achillecalegari/calegari-view-1/docs/img/07_section_three_quarter.jpg

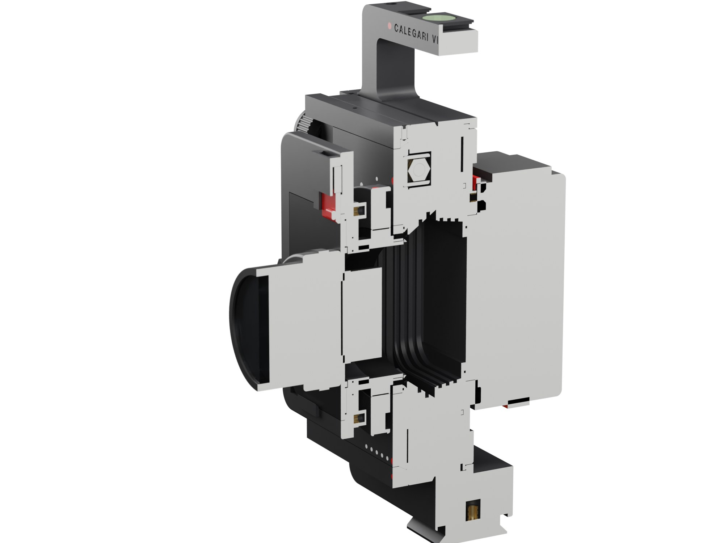
docs/img/07_section_three_quarter.jpg
