achillecalegari/calegari-view-1/print/inlays/x_plate__white.stl

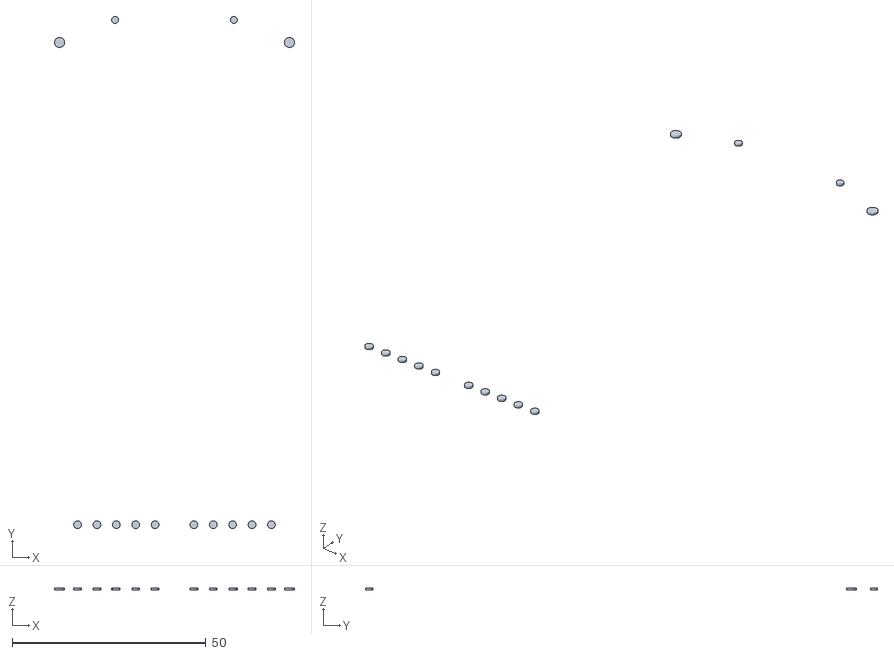
[picture p34: CAD file, 2026-09-28]
print/inlays/x_plate__white.stl
61.9 x 132.1 x 0.6
