achillecalegari/calegari-view-1/print/plates/plate_06_black.3mf

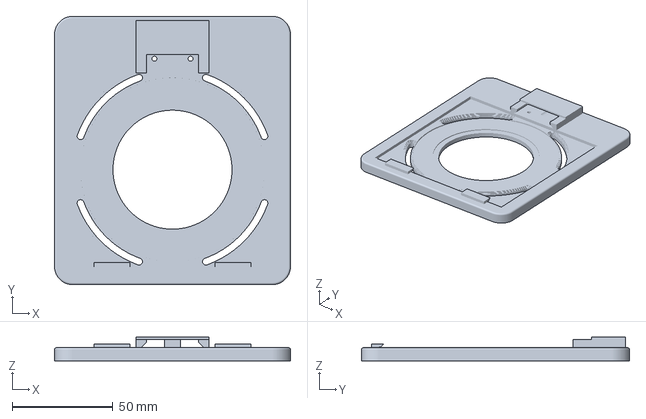
[picture p35: CAD file, 2026-09-28]
print/plates/plate_06_black.3mf
117.0 x 133.0 x 11.7 mm
