achillecalegari/calegari-view-1/print/step/way_y_gib.step

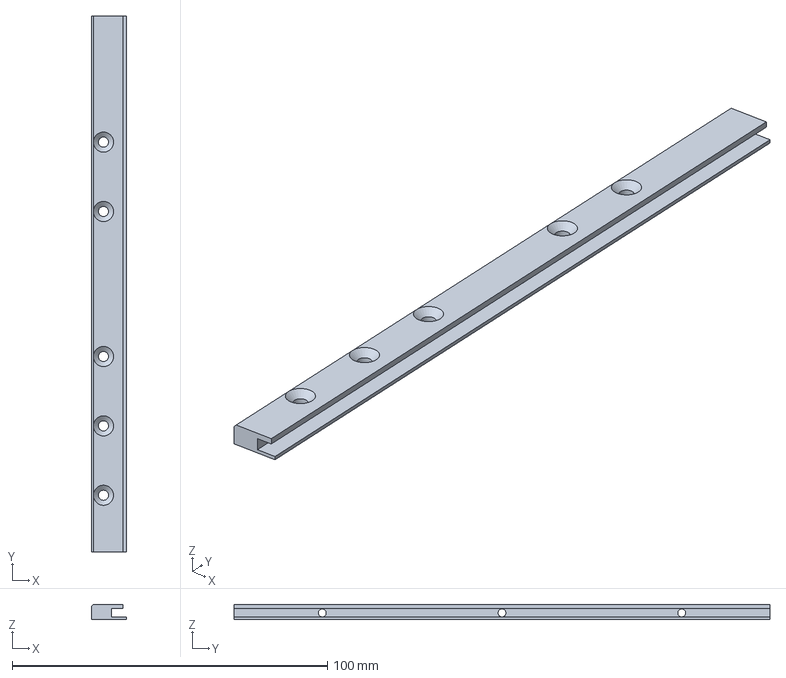
[picture p36: CAD file, 2026-09-28]
print/step/way_y_gib.step
11.0 x 170.0 x 4.80 mm
