achillecalegari/calegari-view-1/print/stl/copal0_shim_0.6mm.stl

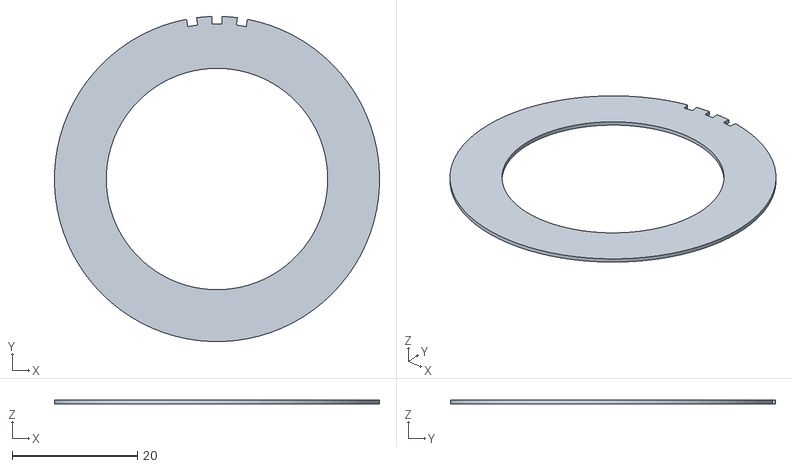
[picture p37: CAD file, 2026-09-27]
print/stl/copal0_shim_0.6mm.stl
52.0 x 52.0 x 0.6
