achillecalegari/calegari-view-1/print/test/coupon_lip_x_bottom.stl

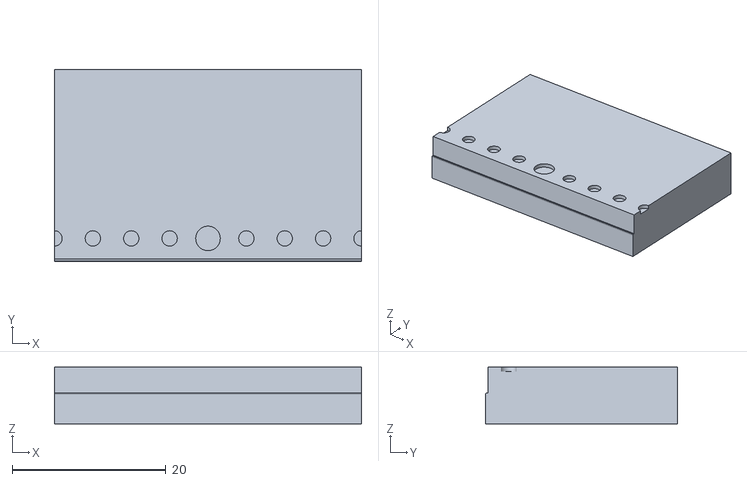
[picture p38: CAD file, 2026-09-28]
print/test/coupon_lip_x_bottom.stl
40.0 x 25.0 x 7.40
