achillecalegari/calegari-view-1/print/inlays/x_plate__red.stl

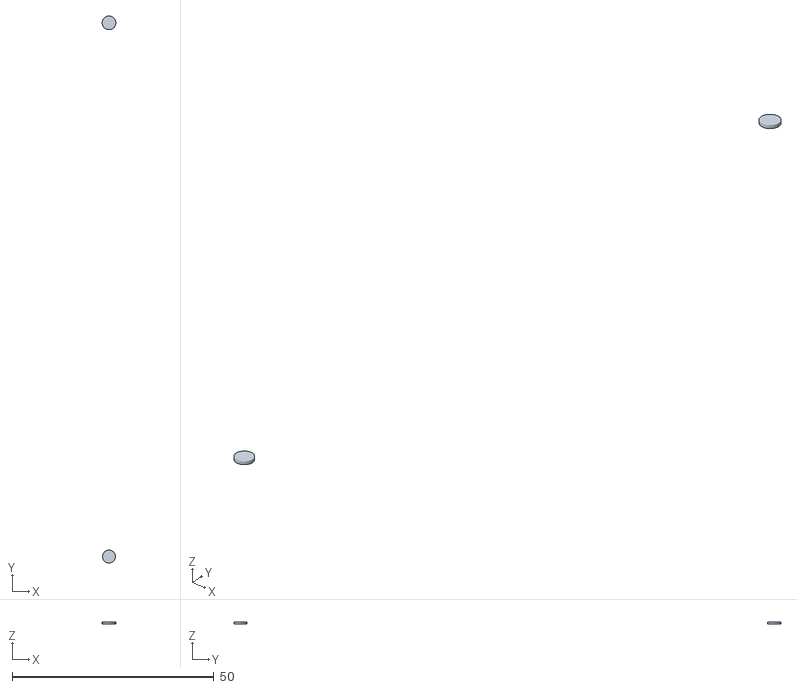
[picture p39: CAD file, 2026-09-28]
print/inlays/x_plate__red.stl
3.40 x 135.5 x 0.6
