achillecalegari/calegari-view-1/print/plates/plate_04_black.3mf

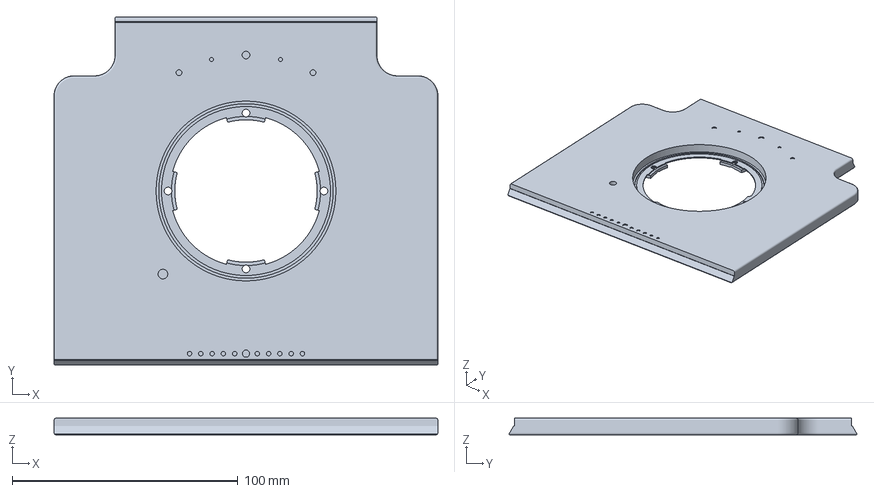
[picture p40: CAD file, 2026-09-28]
print/plates/plate_04_black.3mf
170.0 x 154.0 x 7.40 mm
