achillecalegari/calegari-view-1/print/step/way_x_fixed.step

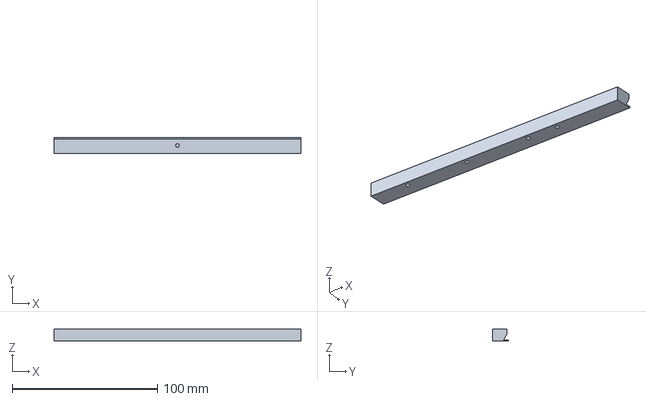
[picture p41: CAD file, 2026-09-28]
print/step/way_x_fixed.step
170.0 x 11.0 x 8.20 mm
