achillecalegari/calegari-view-1/print/stl/copal0_shim_0.4mm.stl

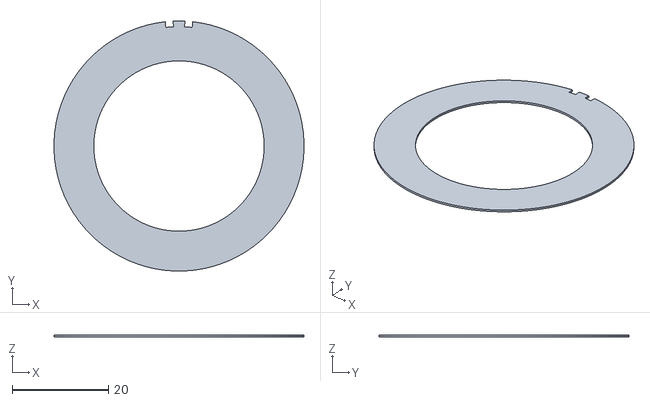
[picture p42: CAD file, 2026-09-27]
print/stl/copal0_shim_0.4mm.stl
52.0 x 52.0 x 0.4
