achillecalegari/calegari-view-1/print/test/coupon_way_y_gib.stl

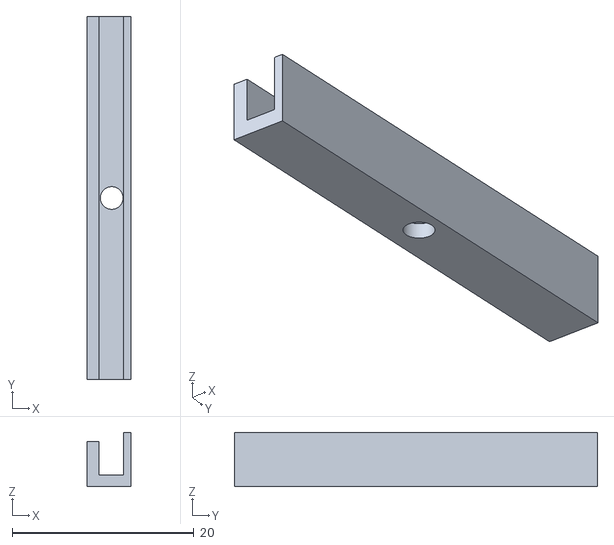
[picture p43: CAD file, 2026-09-28]
print/test/coupon_way_y_gib.stl
4.80 x 40.0 x 6.00
