achillecalegari/calegari-view-1/print/inlays/bezel__white.stl

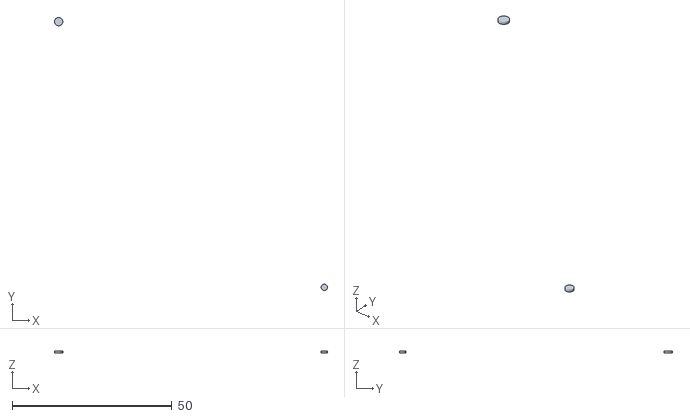
[picture p44: CAD file, 2026-09-28]
print/inlays/bezel__white.stl
85.5 x 85.5 x 0.6
