achillecalegari/calegari-view-1/print/plates/plate_red_1.3mf

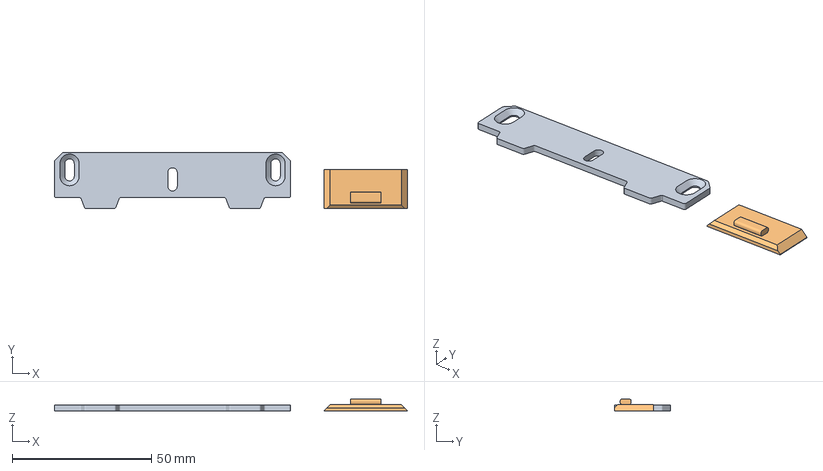
[picture p45: CAD file, 2026-09-28]
print/plates/plate_red_1.3mf
126.8 x 20.1 x 4.40 mm
graflok_blade
holder_latch
