achillecalegari/calegari-view-1/print/step/top_handle.step

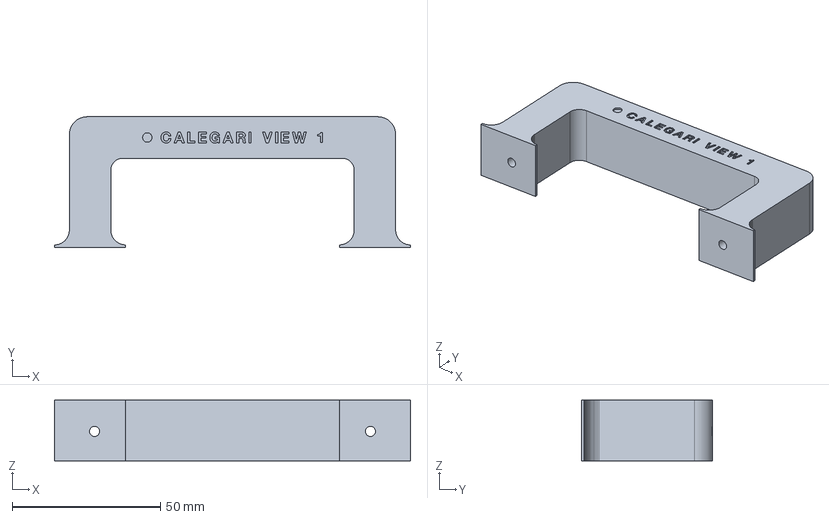
[picture p46: CAD file, 2026-09-28]
print/step/top_handle.step
120.0 x 44.0 x 20.4 mm
