achillecalegari/calegari-view-1/print/test/coupon_way_x_fixed.stl

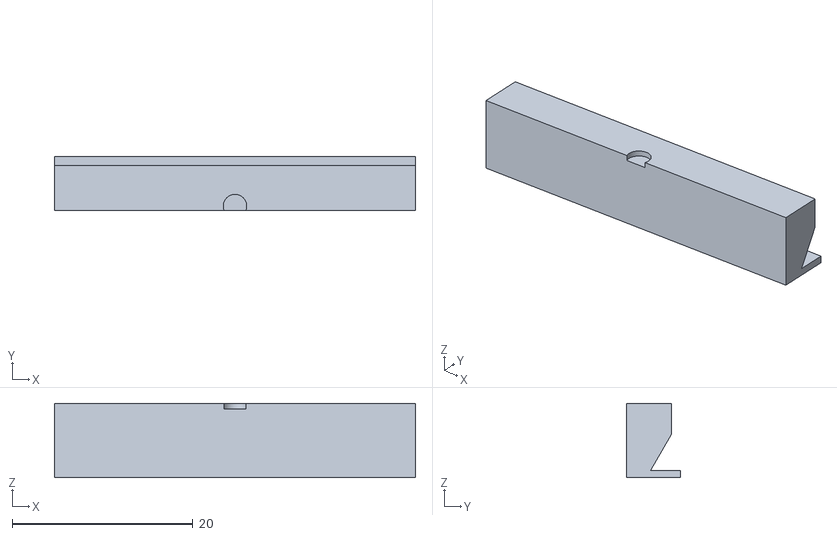
[picture p47: CAD file, 2026-09-28]
print/test/coupon_way_x_fixed.stl
40.0 x 6.00 x 8.20
