achillecalegari/calegari-view-1/print/inlays/knob__red.stl

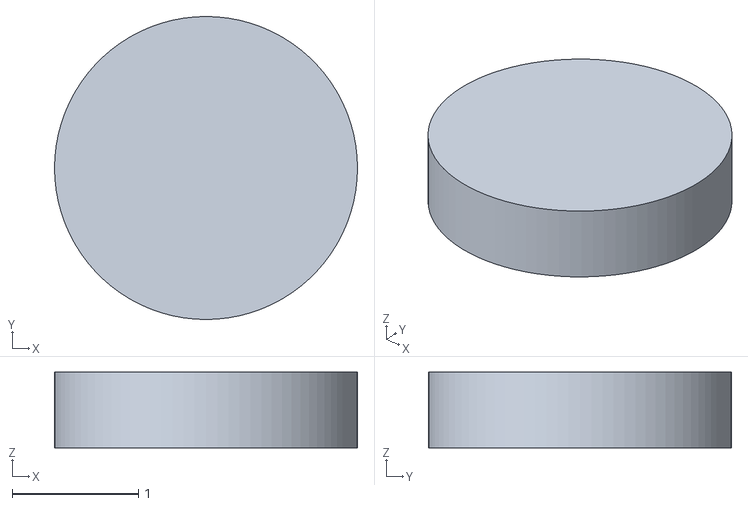
[picture p48: CAD file, 2026-09-28]
print/inlays/knob__red.stl
2.40 x 2.40 x 0.6
