achillecalegari/calegari-view-1/print/step/x_turret.step

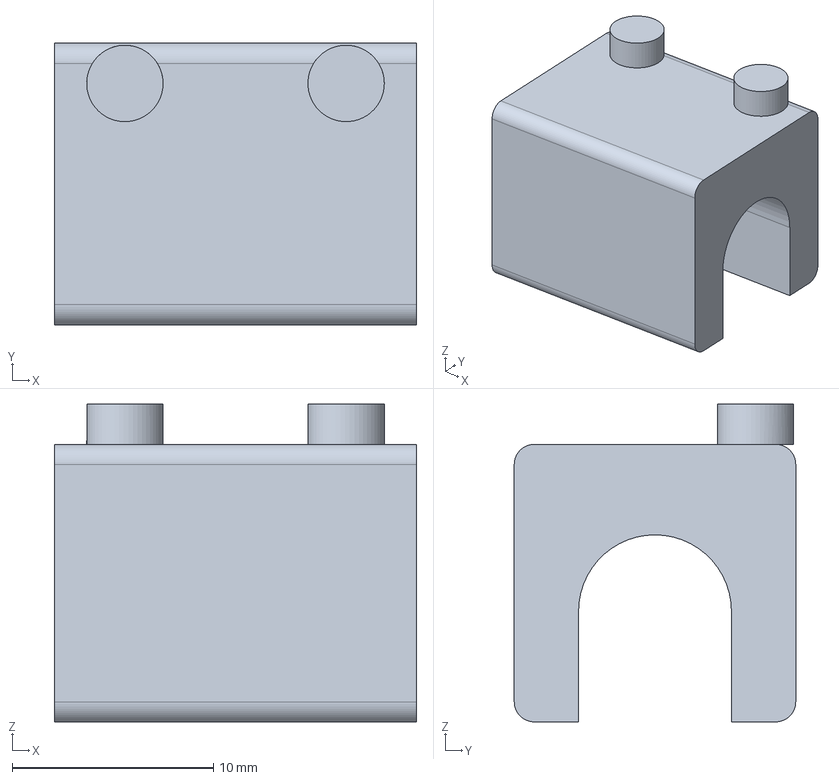
[picture p49: CAD file, 2026-09-28]
print/step/x_turret.step
18.0 x 14.0 x 15.8 mm
