achillecalegari/calegari-view-1/print/test/coupon_way_x_gib.stl

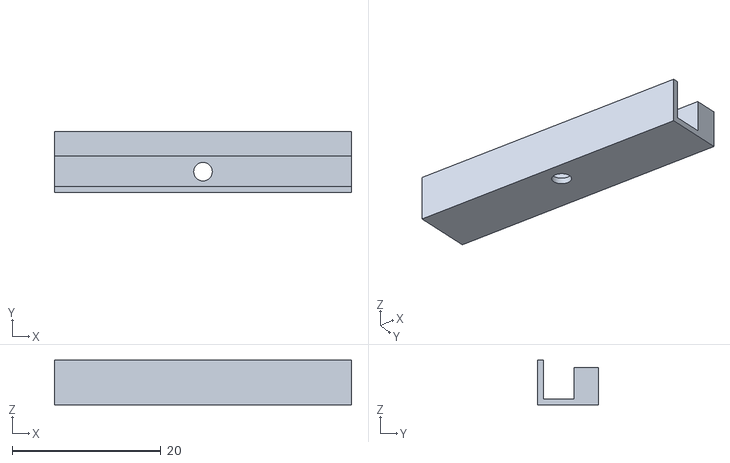
[picture p50: CAD file, 2026-09-28]
print/test/coupon_way_x_gib.stl
40.0 x 8.20 x 6.00
