achillecalegari/calegari-view-1/print/plates/plate_03_black.3mf

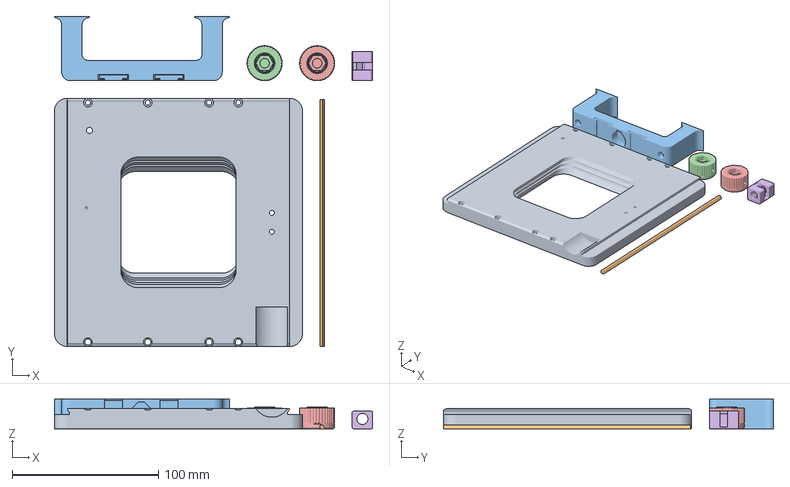
[picture p51: CAD file, 2026-09-28]
print/plates/plate_03_black.3mf
218.0 x 226.0 x 20.4 mm
y_plate
gib_y
top_handle
knob_1
knob_2
y_turret
