achillecalegari/calegari-view-1/print/step/y_turret.step

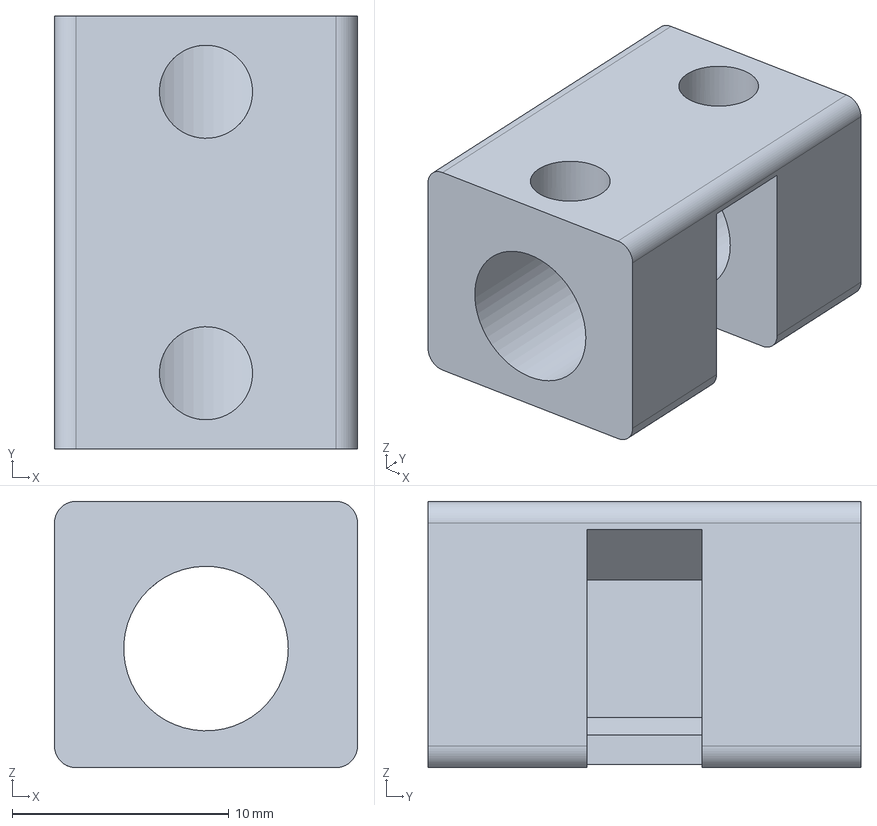
[picture p52: CAD file, 2026-09-28]
print/step/y_turret.step
14.0 x 20.0 x 12.3 mm
