achillecalegari/calegari-view-1/print/plates/plate_00a_shrink_gauge.3mf

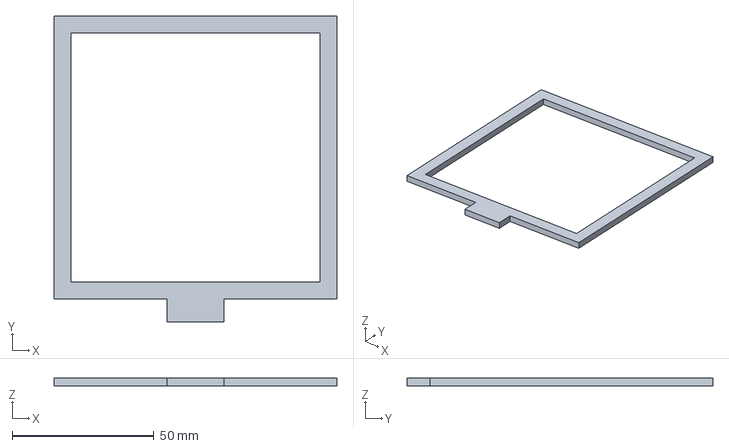
[picture p53: CAD file, 2026-09-28]
print/plates/plate_00a_shrink_gauge.3mf
100.0 x 108.0 x 3.00 mm
