achillecalegari/calegari-view-1/print/step/adapter_ring.step

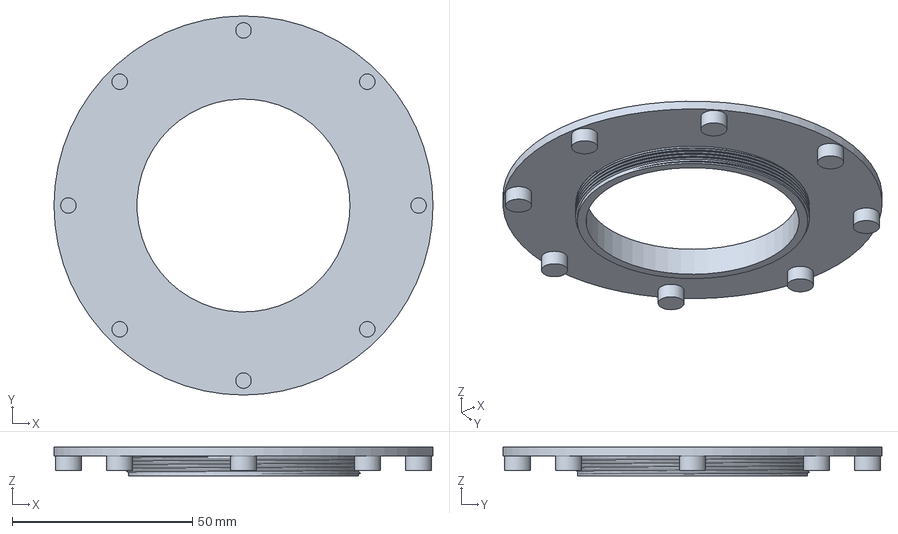
[picture p54: CAD file, 2026-09-28]
print/step/adapter_ring.step
105.0 x 105.0 x 8.00 mm
