achillecalegari/calegari-view-1/print/test/coupon_lip_x_top.stl

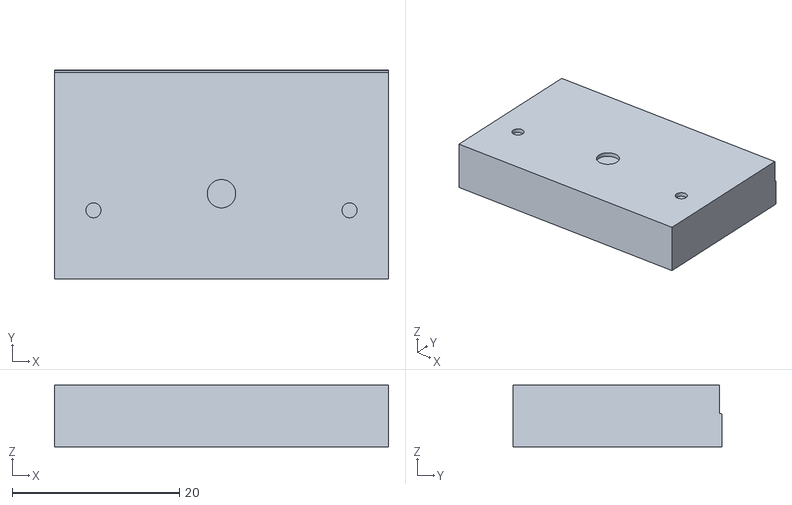
[picture p55: CAD file, 2026-09-28]
print/test/coupon_lip_x_top.stl
40.0 x 25.0 x 7.40
