achillecalegari/calegari-view-1/print/plates/plate_07_shims_0.2mm_layers.3mf

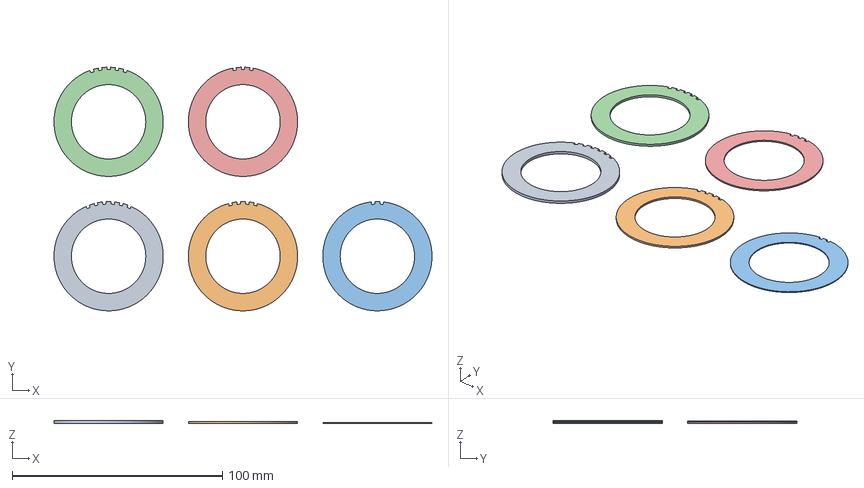
[picture p56: CAD file, 2026-09-28]
print/plates/plate_07_shims_0.2mm_layers.3mf
179.9 x 115.9 x 1.20 mm
copal0_shim_1.2mm
copal0_shim_0.8mm
copal0_shim_0.4mm
copal0_shim_1.0mm
copal0_shim_0.6mm
