achillecalegari/calegari-view-1/print/step/y_plate.step

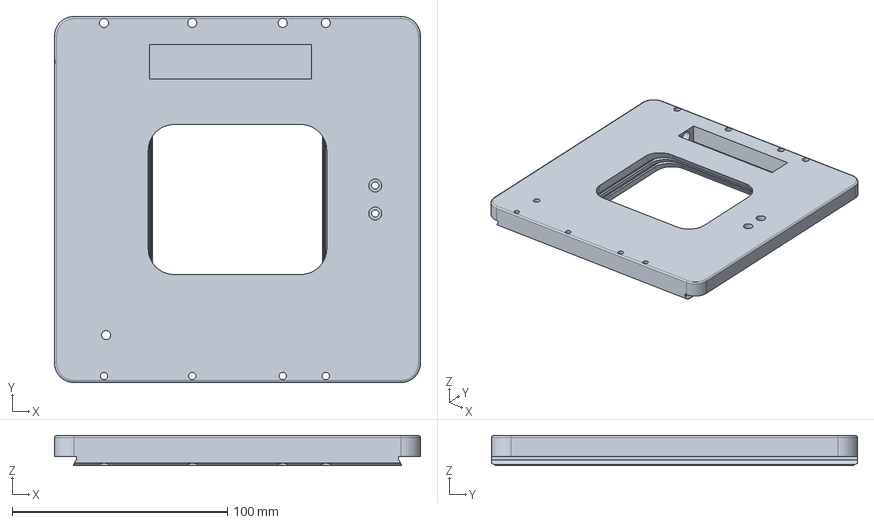
[picture p57: CAD file, 2026-09-28]
print/step/y_plate.step
170.0 x 170.0 x 14.0 mm
