achillecalegari/calegari-view-1/print/test/coupon_way_y_fixed.stl

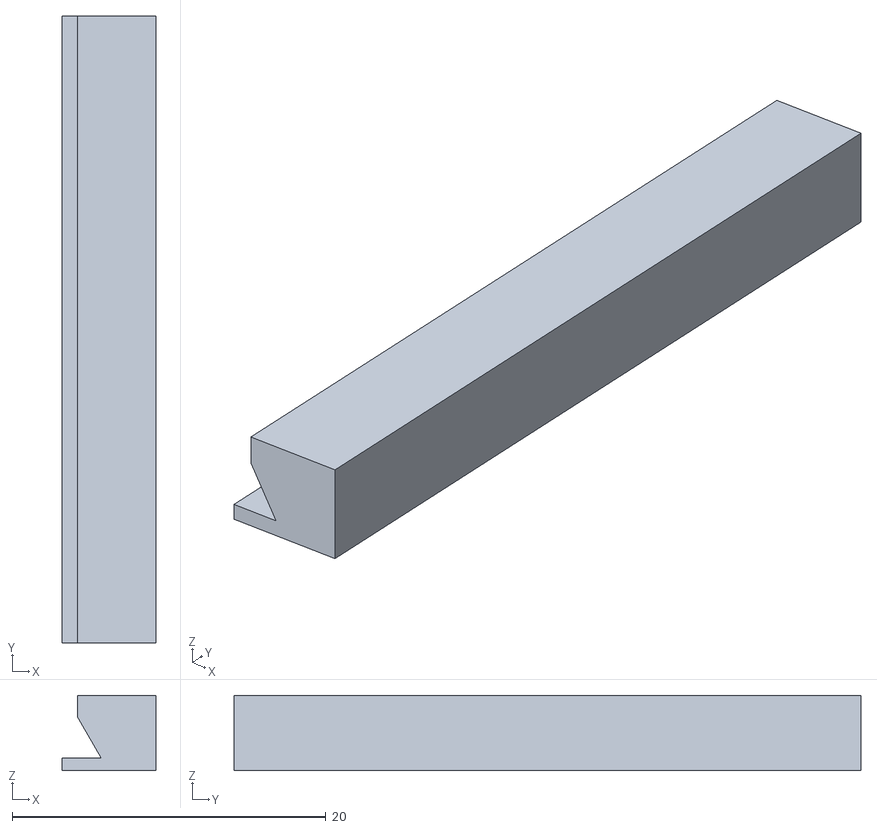
[picture p58: CAD file, 2026-09-28]
print/test/coupon_way_y_fixed.stl
6.00 x 40.0 x 4.80
