achillecalegari/calegari-view-1/print/plates/plate_00b_test_1.3mf

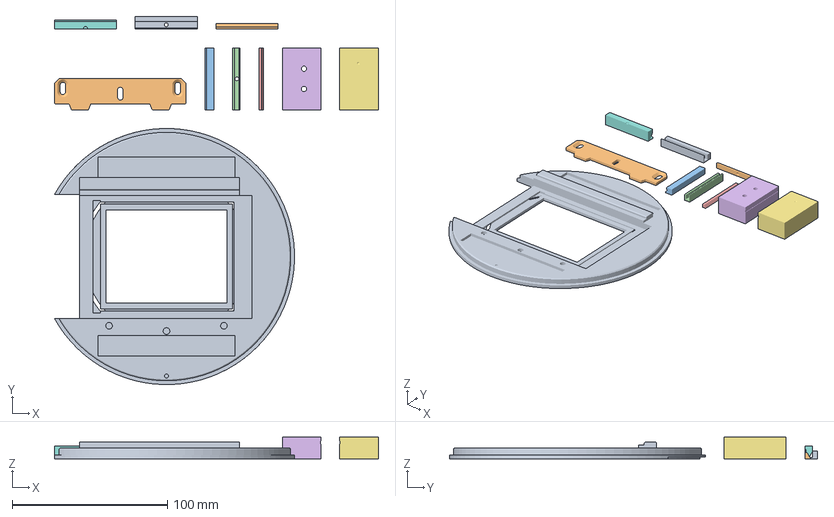
[picture p59: CAD file, 2026-09-28]
print/plates/plate_00b_test_1.3mf
208.7 x 237.2 x 14.0 mm
rotator
graflok_blade
coupon_way_y_fixed
coupon_way_y_gib
coupon_gib_y
coupon_lip_y_left
coupon_lip_y_right
coupon_way_x_fixed
coupon_way_x_gib
coupon_gib_x
