achillecalegari/calegari-view-1/print/step/graflok_wheel.step

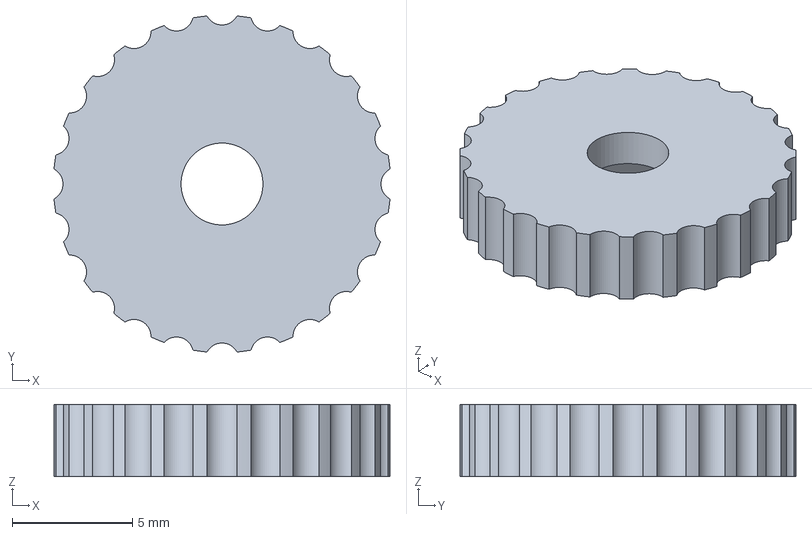
[picture p60: CAD file, 2026-09-28]
print/step/graflok_wheel.step
13.9 x 13.9 x 3.00 mm
