achillecalegari/calegari-view-1/print/test/coupon_gib_y.stl

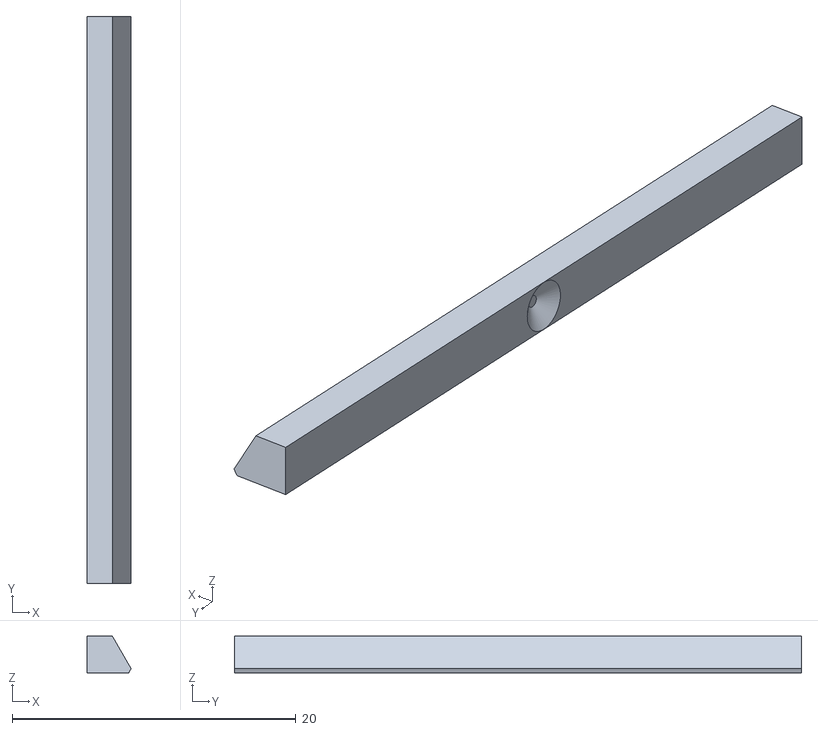
[picture p61: CAD file, 2026-09-28]
print/test/coupon_gib_y.stl
3.13 x 40.0 x 2.60
