achillecalegari/calegari-view-1/print/plates/plate_02_black.3mf

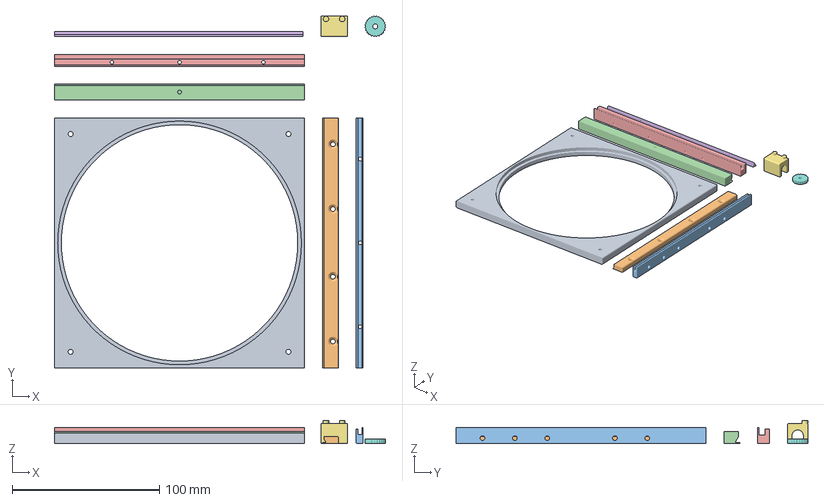
[picture p62: CAD file, 2026-09-28]
print/plates/plate_02_black.3mf
224.9 x 239.2 x 15.8 mm
bezel
way_y_fixed
way_y_gib
way_x_fixed
way_x_gib
gib_x
x_turret
graflok_wheel
