achillecalegari/calegari-view-1/print/step/gib_y.step

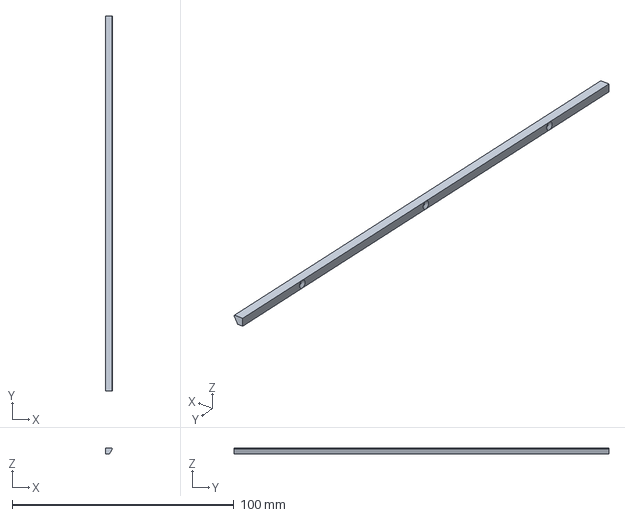
[picture p63: CAD file, 2026-09-28]
print/step/gib_y.step
3.13 x 169.0 x 2.60 mm
