achillecalegari/calegari-view-1/print/plates/plate_07_black_0.12mm_layers.3mf

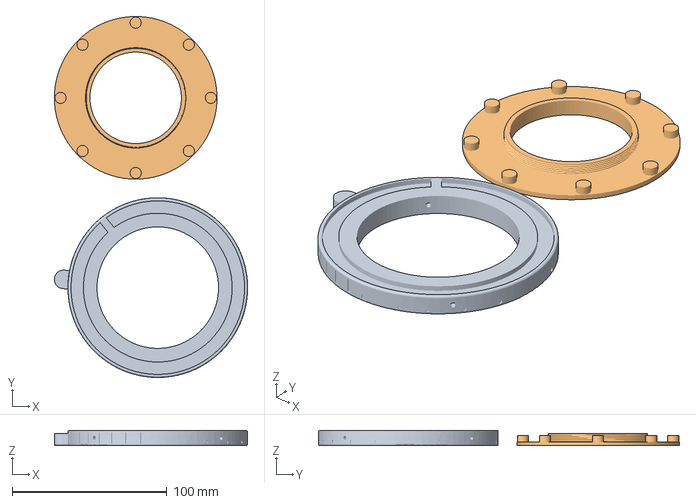
[picture p64: CAD file, 2026-09-28]
print/plates/plate_07_black_0.12mm_layers.3mf
124.8 x 233.0 x 10.0 mm
focus_ring
adapter_ring
