achillecalegari/calegari-view-1/print/step/way_x_gib.step

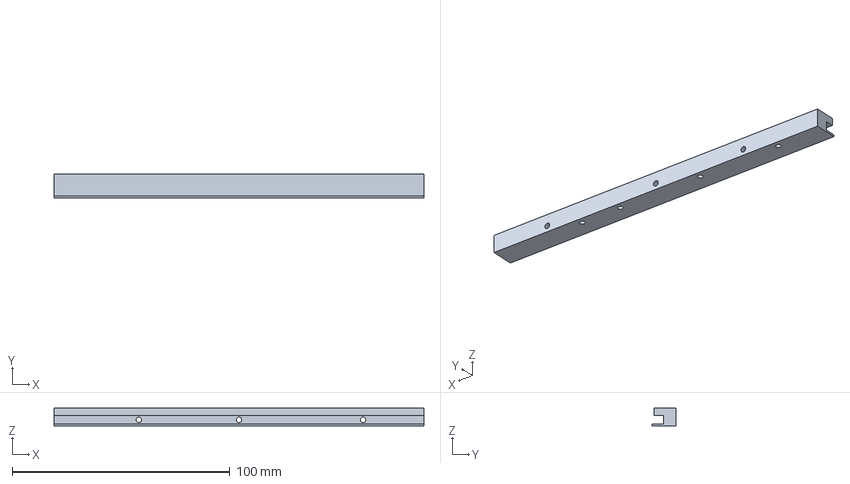
[picture p65: CAD file, 2026-09-28]
print/step/way_x_gib.step
170.0 x 11.0 x 8.20 mm
