achillecalegari/calegari-view-1/print/test/coupon_gib_x.stl

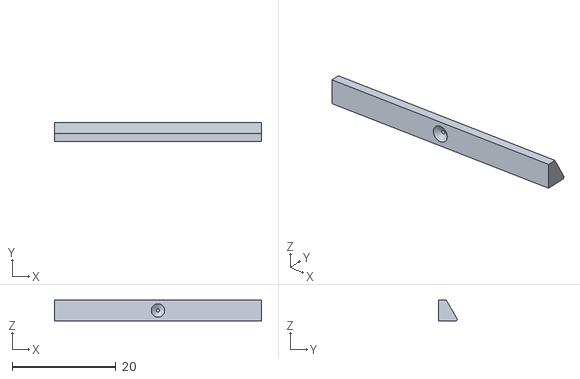
[picture p66: CAD file, 2026-09-28]
print/test/coupon_gib_x.stl
40.0 x 3.64 x 4.00
