achillecalegari/calegari-view-1/print/step/graflok_blade.step

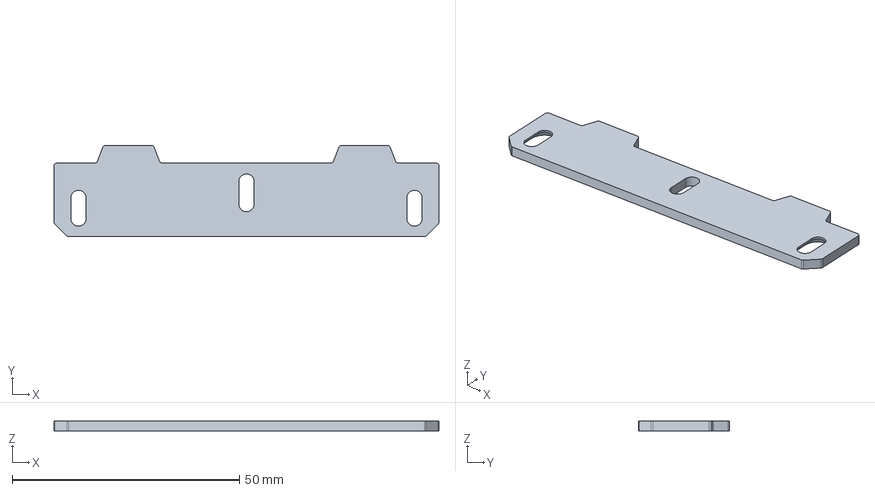
[picture p67: CAD file, 2026-09-28]
print/step/graflok_blade.step
84.8 x 20.1 x 2.20 mm
