achillecalegari/calegari-view-1/print/step/gib_x.step

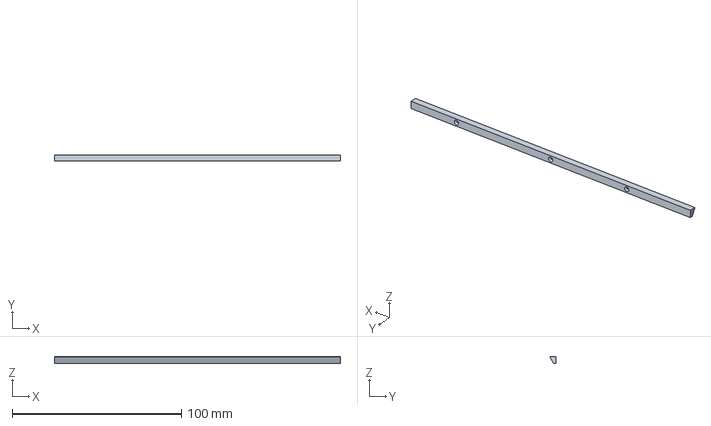
[picture p68: CAD file, 2026-09-28]
print/step/gib_x.step
169.0 x 3.64 x 4.00 mm
