achillecalegari/calegari-view-1/print/step/way_y_fixed.step

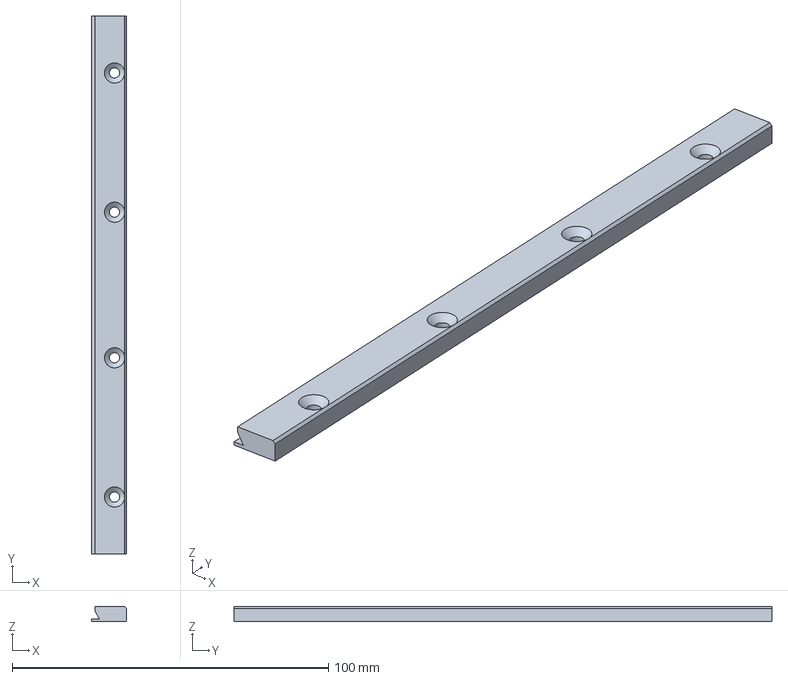
[picture p69: CAD file, 2026-09-28]
print/step/way_y_fixed.step
11.0 x 170.0 x 4.80 mm
