achillecalegari/calegari-view-1/print/step/holder_latch.step

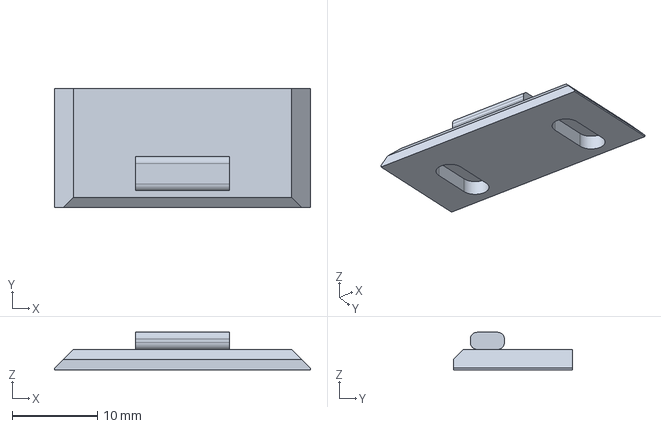
[picture p70: CAD file, 2026-09-28]
print/step/holder_latch.step
30.0 x 14.0 x 4.40 mm
