achillecalegari/calegari-view-1/print/step/bezel.step

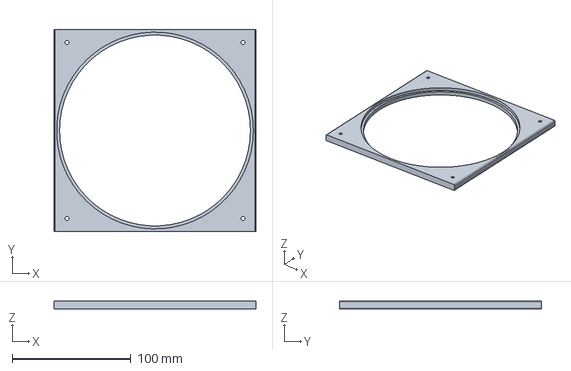
[picture p71: CAD file, 2026-09-28]
print/step/bezel.step
170.0 x 170.0 x 7.10 mm
