achillecalegari/calegari-view-1/docs/img/step_01.jpg

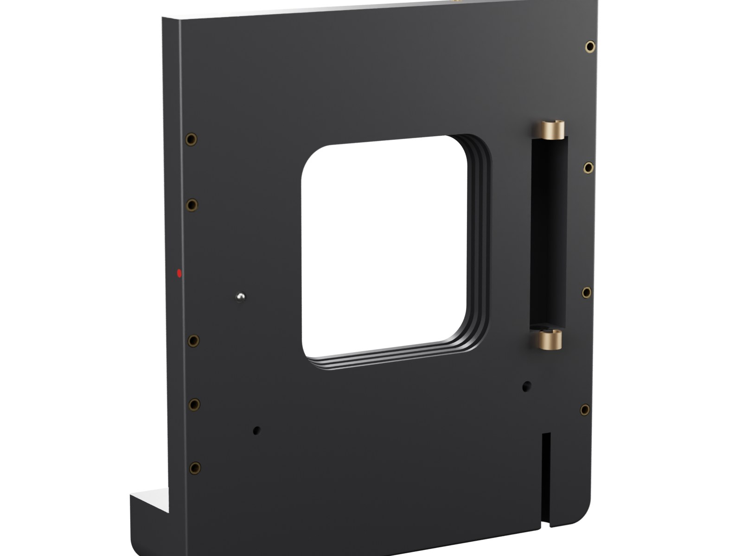
docs/img/step_01.jpg
