achillecalegari/calegari-view-1/docs/img/step_03.jpg

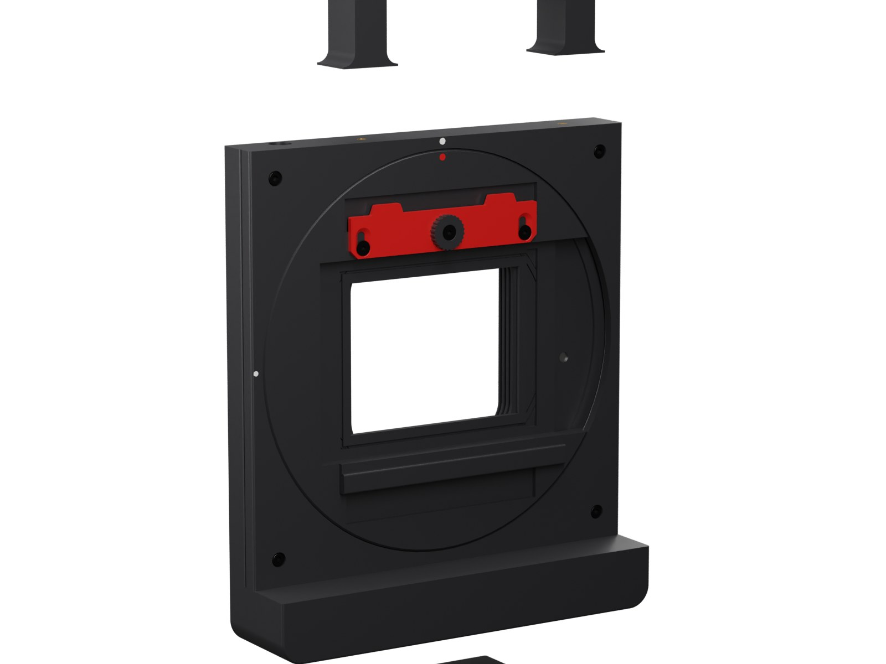
docs/img/step_03.jpg
