achillecalegari/calegari-view-1/docs/img/step_05.jpg

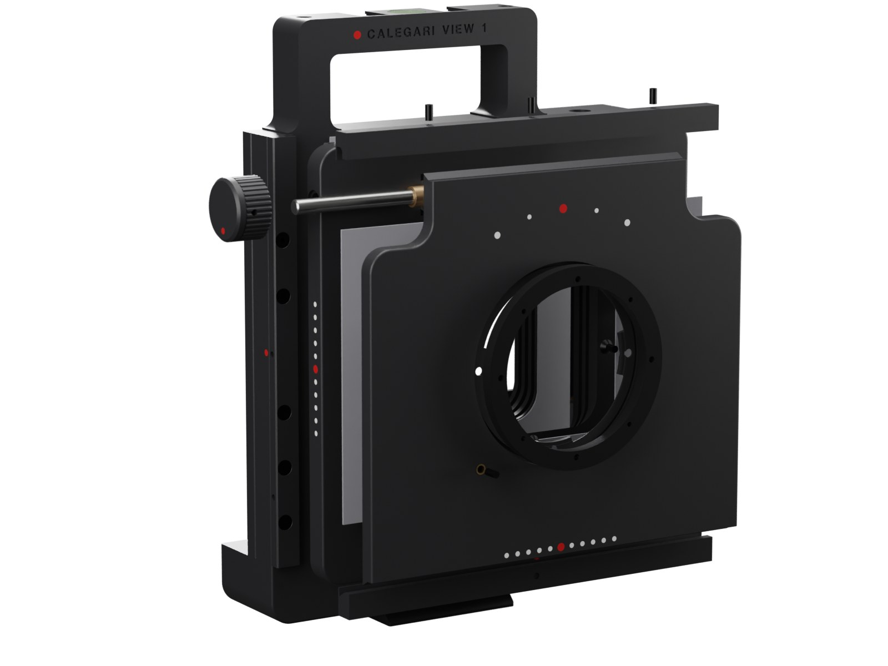
docs/img/step_05.jpg
