achillecalegari/calegari-view-1/docs/img/step_07.jpg

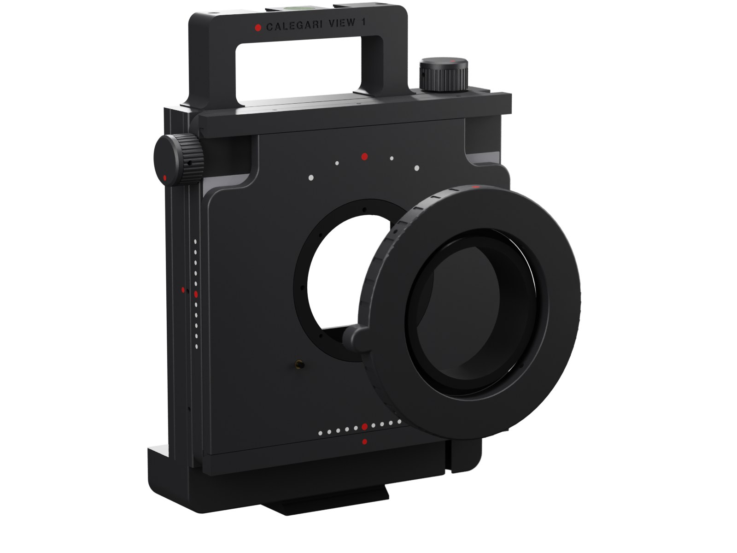
docs/img/step_07.jpg
