achillecalegari/calegari-view-1/docs/img/step_08.jpg

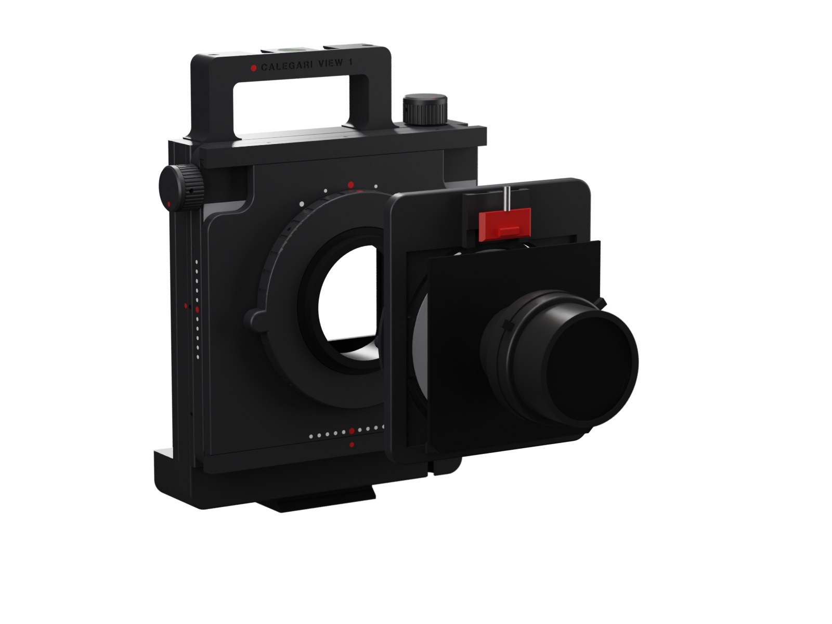
docs/img/step_08.jpg
